slashbyte/ChessComputer/photo/photo01.jpg

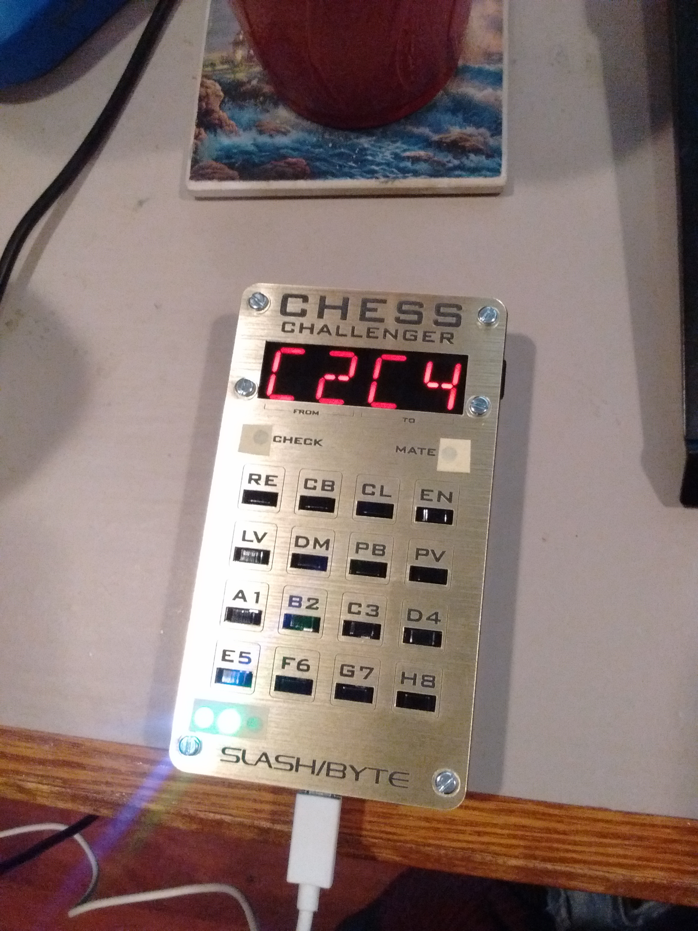
photo/photo01.jpg
