slashbyte/ChessComputer/photo/photo02.jpg

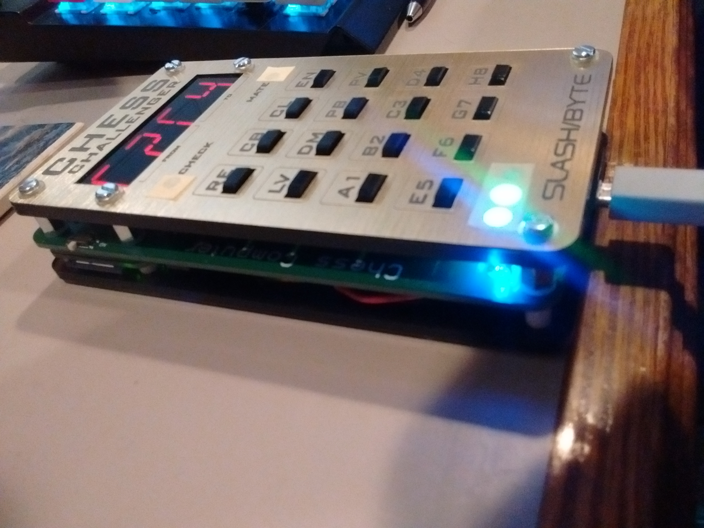
photo/photo02.jpg
