slashbyte/ChessComputer/assembly/guide/bottom-iso.png

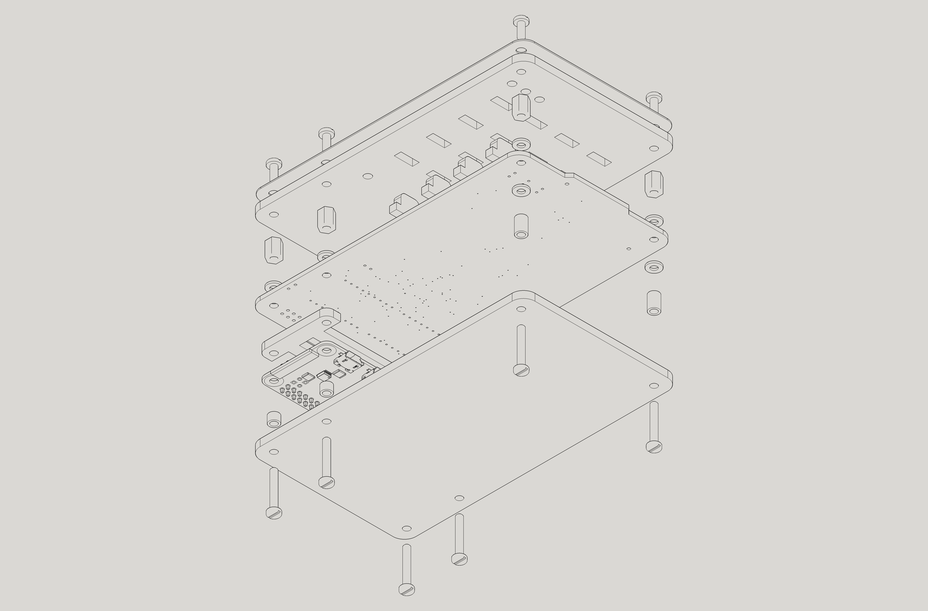
assembly/guide/bottom-iso.png
