slashbyte/ChessComputer/assembly/guide/front.png

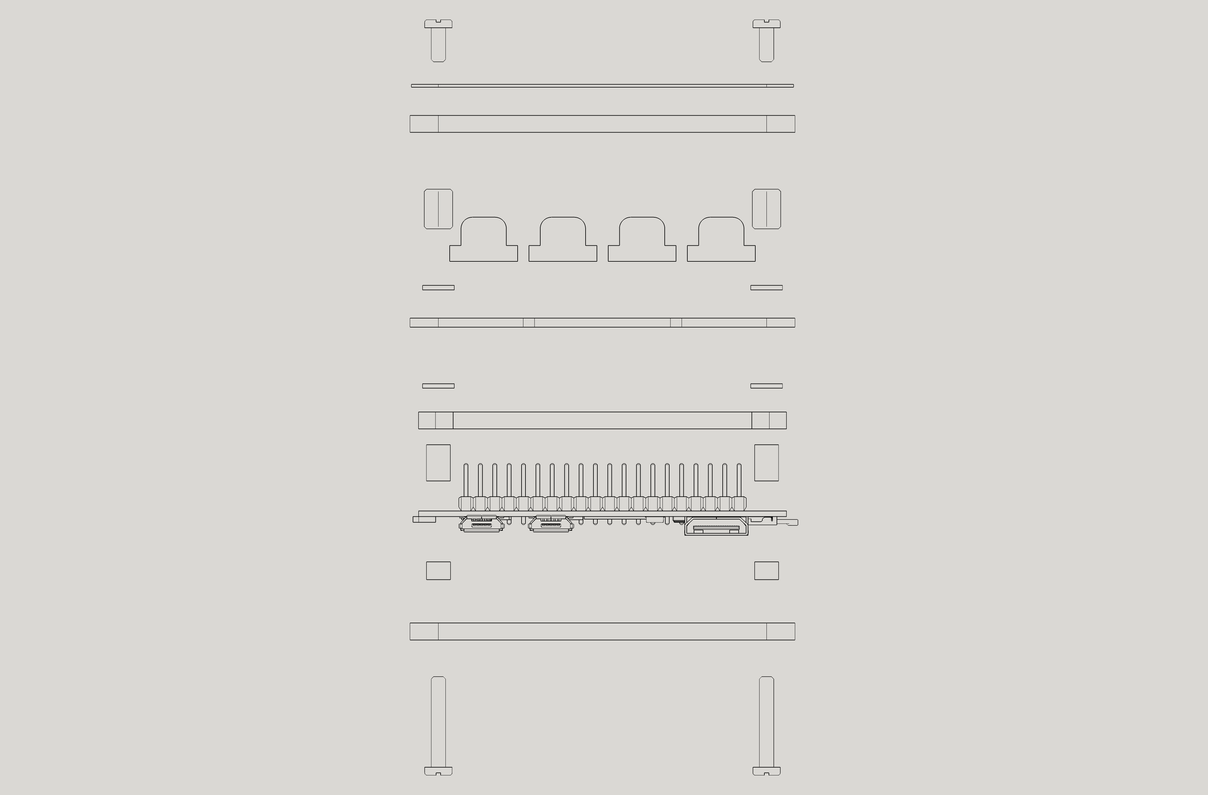
assembly/guide/front.png
