slashbyte/ChessComputer/assembly/guide/left.png

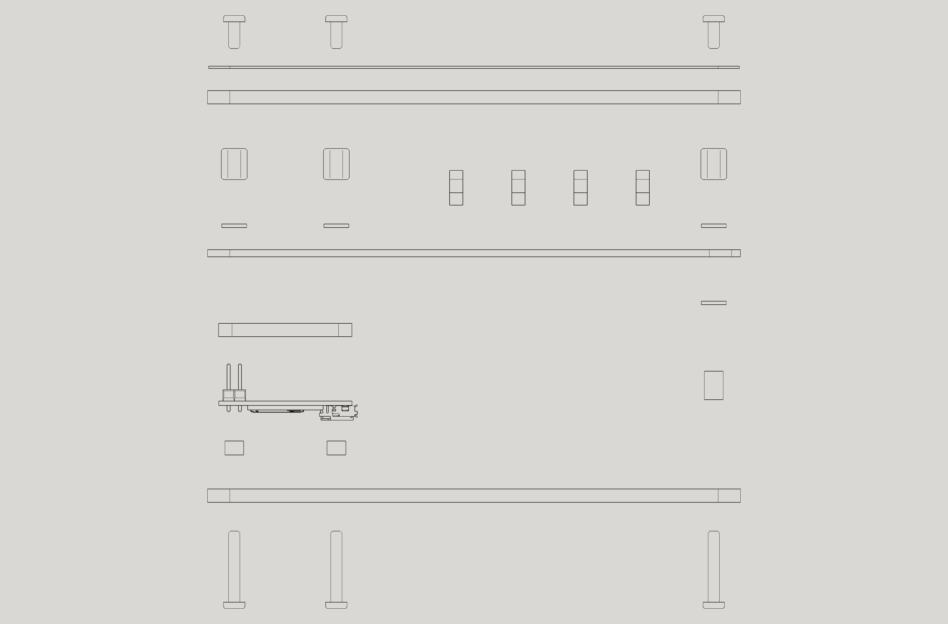
assembly/guide/left.png
