slashbyte/ChessComputer/assembly/guide/top-iso.png

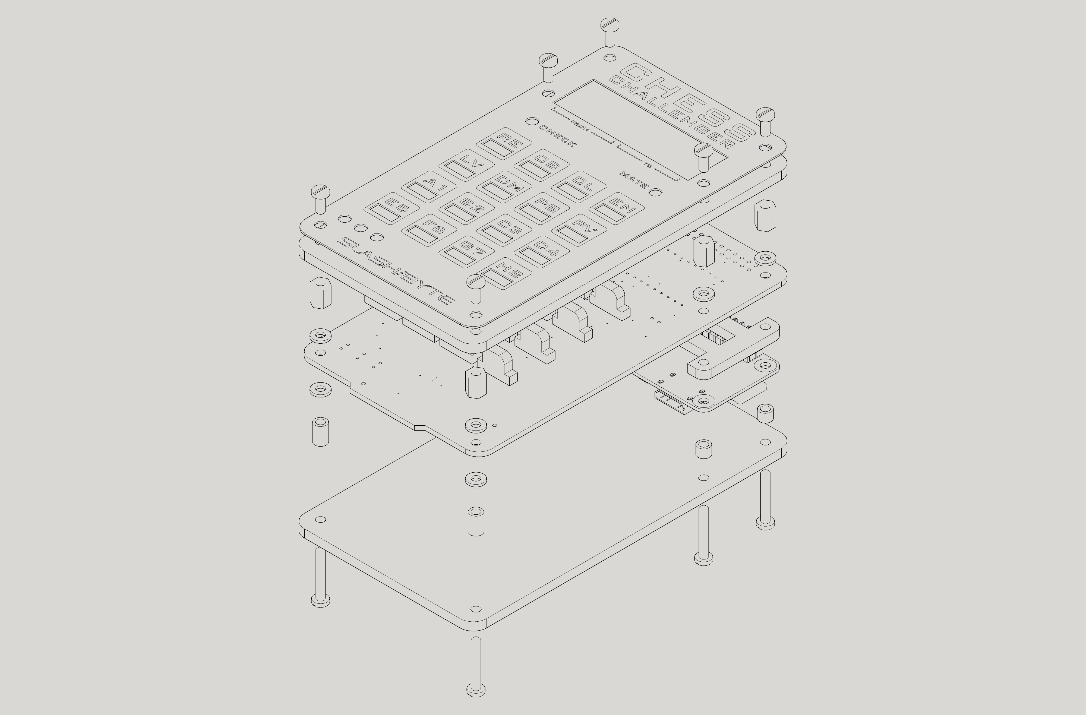
assembly/guide/top-iso.png
